IzeHouze/A-10C-UFC/A-10CV1.2/A-10C-CautionLED/A-10C-CautionLEDLEDSide.png

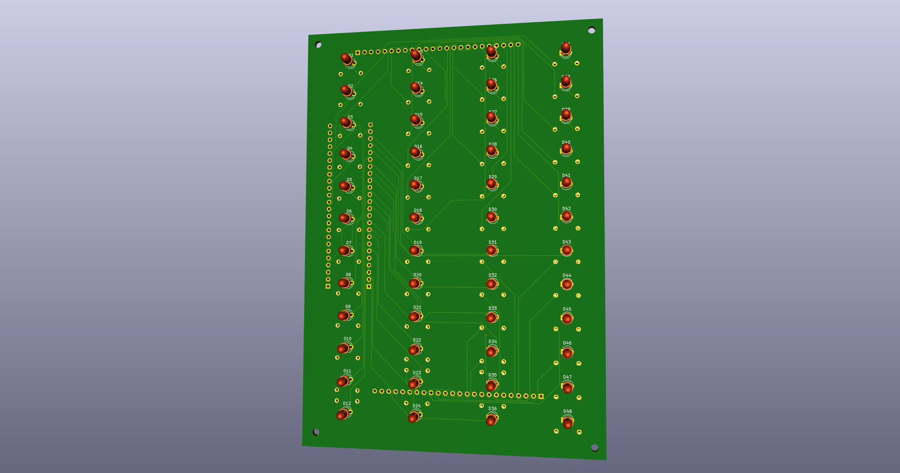
A-10CV1.2/A-10C-CautionLED/A-10C-CautionLEDLEDSide.png
