IzeHouze/A-10C-UFC/A-10CV1.2/A-10C-CautionPanelNonMega/A-10C-CautionPanelNonMegaConnectorSide.png

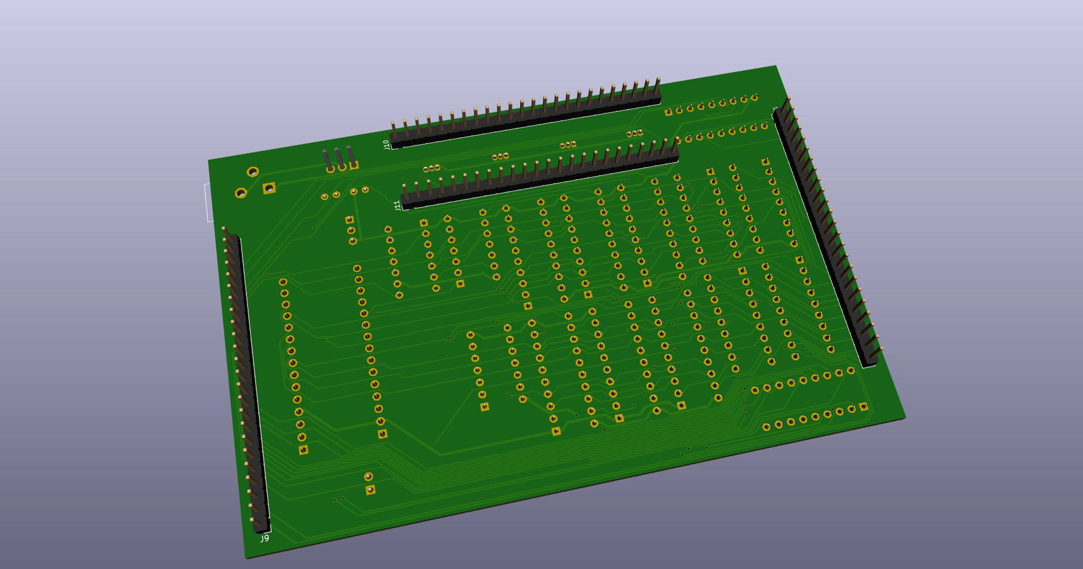
A-10CV1.2/A-10C-CautionPanelNonMega/A-10C-CautionPanelNonMegaConnectorSide.png
